Hakman482/fpga-power-quality-monitor/hardware/kicad/myProject_models/M20-9990446_debug.step

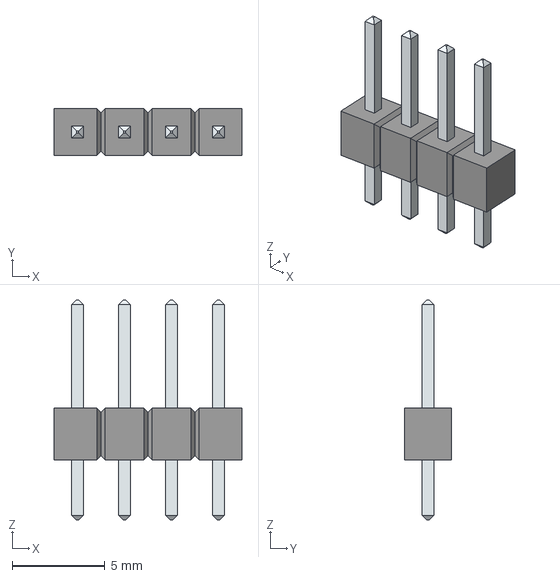
[picture p33: CAD file, 2026-09-30]
hardware/kicad/myProject_models/M20-9990446_debug.step
10.2 x 2.54 x 11.9 mm
LeadsArray
