Hakman482/fpga-power-quality-monitor/hardware/kicad/myProject_models/B72214P2271K101MOV.step

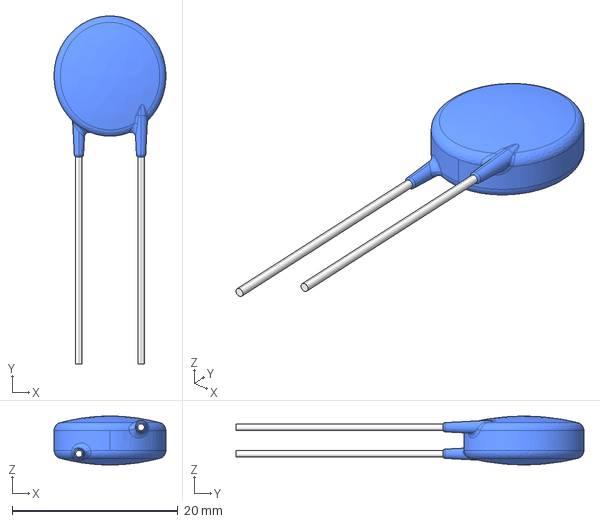
[picture p34: CAD file, 2026-09-30]
hardware/kicad/myProject_models/B72214P2271K101MOV.step
13.5 x 42.0 x 5.90 mm
