Hakman482/fpga-power-quality-monitor/hardware/kicad/myProject_models/L101011MS02Q_pswitch.step

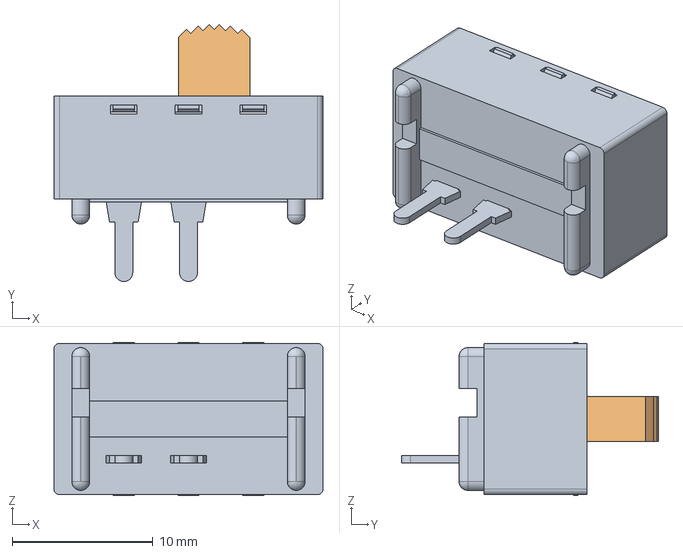
[picture p35: CAD file, 2026-09-30]
hardware/kicad/myProject_models/L101011MS02Q_pswitch.step
19.1 x 18.3 x 10.9 mm
