Hakman482/fpga-power-quality-monitor/validation/current/raw/raw_adc_0.3A.csv

timestamp_utc | frame_sequence | sample_index | sample_time_s | sample_rate_hz | voltage_raw_code | current_raw_code | scaled_voltage_v | scaled_current_a
2026-09-17T15:48:03.453522+00:00 | 383 | 0 | 0 | 10000 | 33043 | 38997 | 3.374 | 0.316526
2026-09-17T15:48:03.453522+00:00 | 383 | 1 | 0.0001 | 10000 | 33043 | 38703 | 3.374 | 0.302507
2026-09-17T15:48:03.453522+00:00 | 383 | 2 | 0.0002 | 10000 | 33043 | 38573 | 3.374 | 0.296308
2026-09-17T15:48:03.453522+00:00 | 383 | 3 | 0.0003 | 10000 | 33033 | 38667 | 3.23 | 0.30079
2026-09-17T15:48:03.453522+00:00 | 383 | 4 | 0.0004 | 10000 | 33047 | 38507 | 3.432 | 0.293161
2026-09-17T15:48:03.453522+00:00 | 383 | 5 | 0.0005 | 10000 | 33031 | 38463 | 3.201 | 0.291063
2026-09-17T15:48:03.453522+00:00 | 383 | 6 | 0.0006 | 10000 | 33042 | 38619 | 3.36 | 0.298501
2026-09-17T15:48:03.453522+00:00 | 383 | 7 | 0.0007 | 10000 | 33041 | 38615 | 3.345 | 0.298311
2026-09-17T15:48:03.453522+00:00 | 383 | 8 | 0.0008 | 10000 | 33037 | 38633 | 3.288 | 0.299169
2026-09-17T15:48:03.453522+00:00 | 383 | 9 | 0.0009 | 10000 | 33039 | 38610 | 3.317 | 0.298072
2026-09-17T15:48:03.453522+00:00 | 383 | 10 | 0.001 | 10000 | 33033 | 38681 | 3.23 | 0.301458
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
