Hakman482/fpga-power-quality-monitor/validation/current/raw/raw_adc_0.45A.csv

timestamp_utc | frame_sequence | sample_index | sample_time_s | sample_rate_hz | voltage_raw_code | current_raw_code | scaled_voltage_v | scaled_current_a
2026-09-17T15:59:47.270800+00:00 | 718 | 0 | 0.000000000 | 10000 | 33141 | 42173 | 4.788000000 | 0.467970000000
2026-09-17T15:59:47.270800+00:00 | 718 | 1 | 0.000100000 | 10000 | 33150 | 41999 | 4.917000000 | 0.459673000000
2026-09-17T15:59:47.270800+00:00 | 718 | 2 | 0.000200000 | 10000 | 33142 | 42219 | 4.802000000 | 0.470164000000
2026-09-17T15:59:47.270800+00:00 | 718 | 3 | 0.000300000 | 10000 | 33143 | 42247 | 4.816000000 | 0.471499000000
2026-09-17T15:59:47.270800+00:00 | 718 | 4 | 0.000400000 | 10000 | 33149 | 42443 | 4.903000000 | 0.480845000000
2026-09-17T15:59:47.270800+00:00 | 718 | 5 | 0.000500000 | 10000 | 33151 | 42383 | 4.932000000 | 0.477984000000
2026-09-17T15:59:47.270800+00:00 | 718 | 6 | 0.000600000 | 10000 | 33149 | 42299 | 4.903000000 | 0.473978000000
2026-09-17T15:59:47.270800+00:00 | 718 | 7 | 0.000700000 | 10000 | 33141 | 42191 | 4.788000000 | 0.468829000000
2026-09-17T15:59:47.270800+00:00 | 718 | 8 | 0.000800000 | 10000 | 33142 | 41941 | 4.802000000 | 0.456908000000
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
