Hakman482/fpga-power-quality-monitor/validation/current/raw/raw_adc_0.4A.csv

timestamp_utc | frame_sequence | sample_index | sample_time_s | sample_rate_hz | voltage_raw_code | current_raw_code | scaled_voltage_v | scaled_current_a
2026-09-17T15:54:46.915726+00:00 | 575 | 0 | 0.000000000 | 10000 | 33105 | 40823 | 4.268000000 | 0.403597000000
2026-09-17T15:54:46.915726+00:00 | 575 | 1 | 0.000100000 | 10000 | 33121 | 40823 | 4.499000000 | 0.403597000000
2026-09-17T15:54:46.915726+00:00 | 575 | 2 | 0.000200000 | 10000 | 33115 | 40951 | 4.413000000 | 0.409700000000
2026-09-17T15:54:46.915726+00:00 | 575 | 3 | 0.000300000 | 10000 | 33117 | 41039 | 4.441000000 | 0.413897000000
2026-09-17T15:54:46.915726+00:00 | 575 | 4 | 0.000400000 | 10000 | 33116 | 40975 | 4.427000000 | 0.410845000000
2026-09-17T15:54:46.915726+00:00 | 575 | 5 | 0.000500000 | 10000 | 33124 | 40923 | 4.542000000 | 0.408365000000
2026-09-17T15:54:46.915726+00:00 | 575 | 6 | 0.000600000 | 10000 | 33119 | 40846 | 4.470000000 | 0.404694000000
2026-09-17T15:54:46.915726+00:00 | 575 | 7 | 0.000700000 | 10000 | 33108 | 40791 | 4.312000000 | 0.402071000000
2026-09-17T15:54:46.915726+00:00 | 575 | 8 | 0.000800000 | 10000 | 33091 | 40869 | 4.067000000 | 0.405790000000
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
