Hakman482/fpga-power-quality-monitor/validation/current/raw/raw_adc_20260917_0.35A.csv

timestamp_utc | frame_sequence | sample_index | sample_time_s | sample_rate_hz | voltage_raw_code | current_raw_code | scaled_voltage_v | scaled_current_a
2026-09-17T15:52:19.893679+00:00 | 505 | 0 | 0.000000000 | 10000 | 33067 | 40161 | 3.720000000 | 0.372030000000
2026-09-17T15:52:19.893679+00:00 | 505 | 1 | 0.000100000 | 10000 | 33079 | 39947 | 3.893000000 | 0.361826000000
2026-09-17T15:52:19.893679+00:00 | 505 | 2 | 0.000200000 | 10000 | 33081 | 39833 | 3.922000000 | 0.356390000000
2026-09-17T15:52:19.893679+00:00 | 505 | 3 | 0.000300000 | 10000 | 33078 | 39821 | 3.879000000 | 0.355818000000
2026-09-17T15:52:19.893679+00:00 | 505 | 4 | 0.000400000 | 10000 | 33077 | 39907 | 3.865000000 | 0.359918000000
2026-09-17T15:52:19.893679+00:00 | 505 | 5 | 0.000500000 | 10000 | 33081 | 40103 | 3.922000000 | 0.369264000000
2026-09-17T15:52:19.893679+00:00 | 505 | 6 | 0.000600000 | 10000 | 33087 | 39735 | 4.009000000 | 0.351717000000
2026-09-17T15:52:19.893679+00:00 | 505 | 7 | 0.000700000 | 10000 | 33071 | 39807 | 3.778000000 | 0.355150000000
2026-09-17T15:52:19.893679+00:00 | 505 | 8 | 0.000800000 | 10000 | 33071 | 40009 | 3.778000000 | 0.364782000000
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
